itacarobotics/Metis2/doc/motors/17HS24-2004D-E1K/17HS24-2004D-E1K_Torque_Curve.pdf

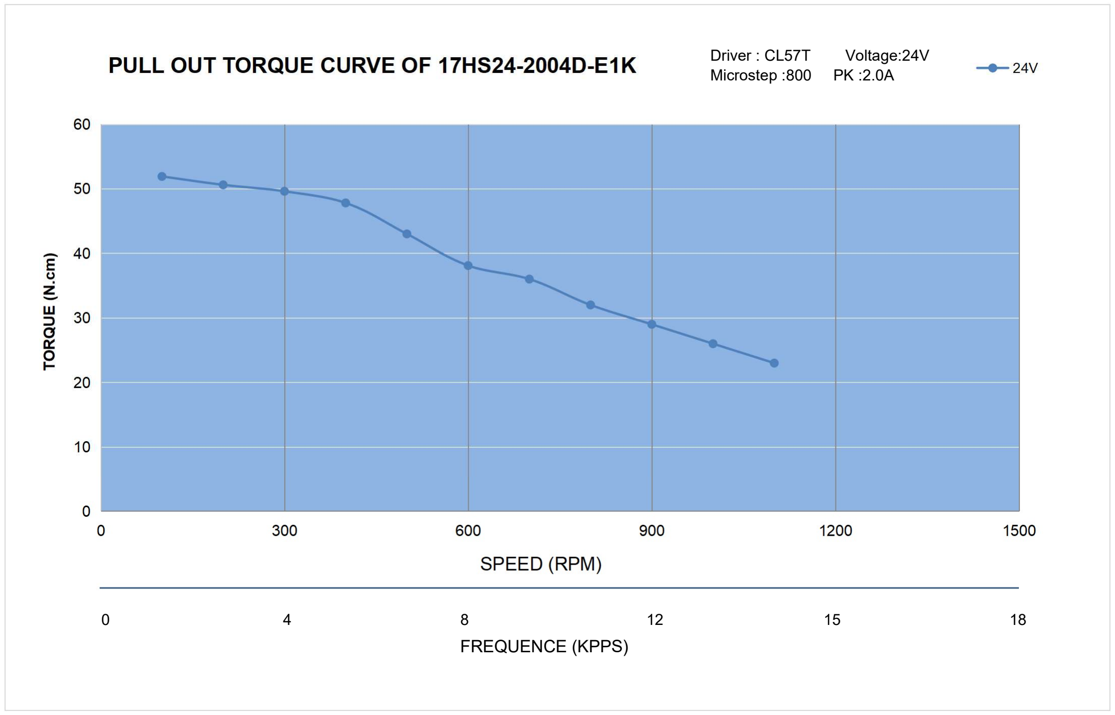
[picture p1: page 1]

Driver : CL57T | Voltage:24V
Microstep :800 | PK :2.0A
0 | 4 | 8 | 12 | 15 | 18
FREQUENCE (KPPS)
