itacarobotics/Metis2/doc/motors/17HS24-2004D-E1K/17HS24-2004D-E1K.pdf

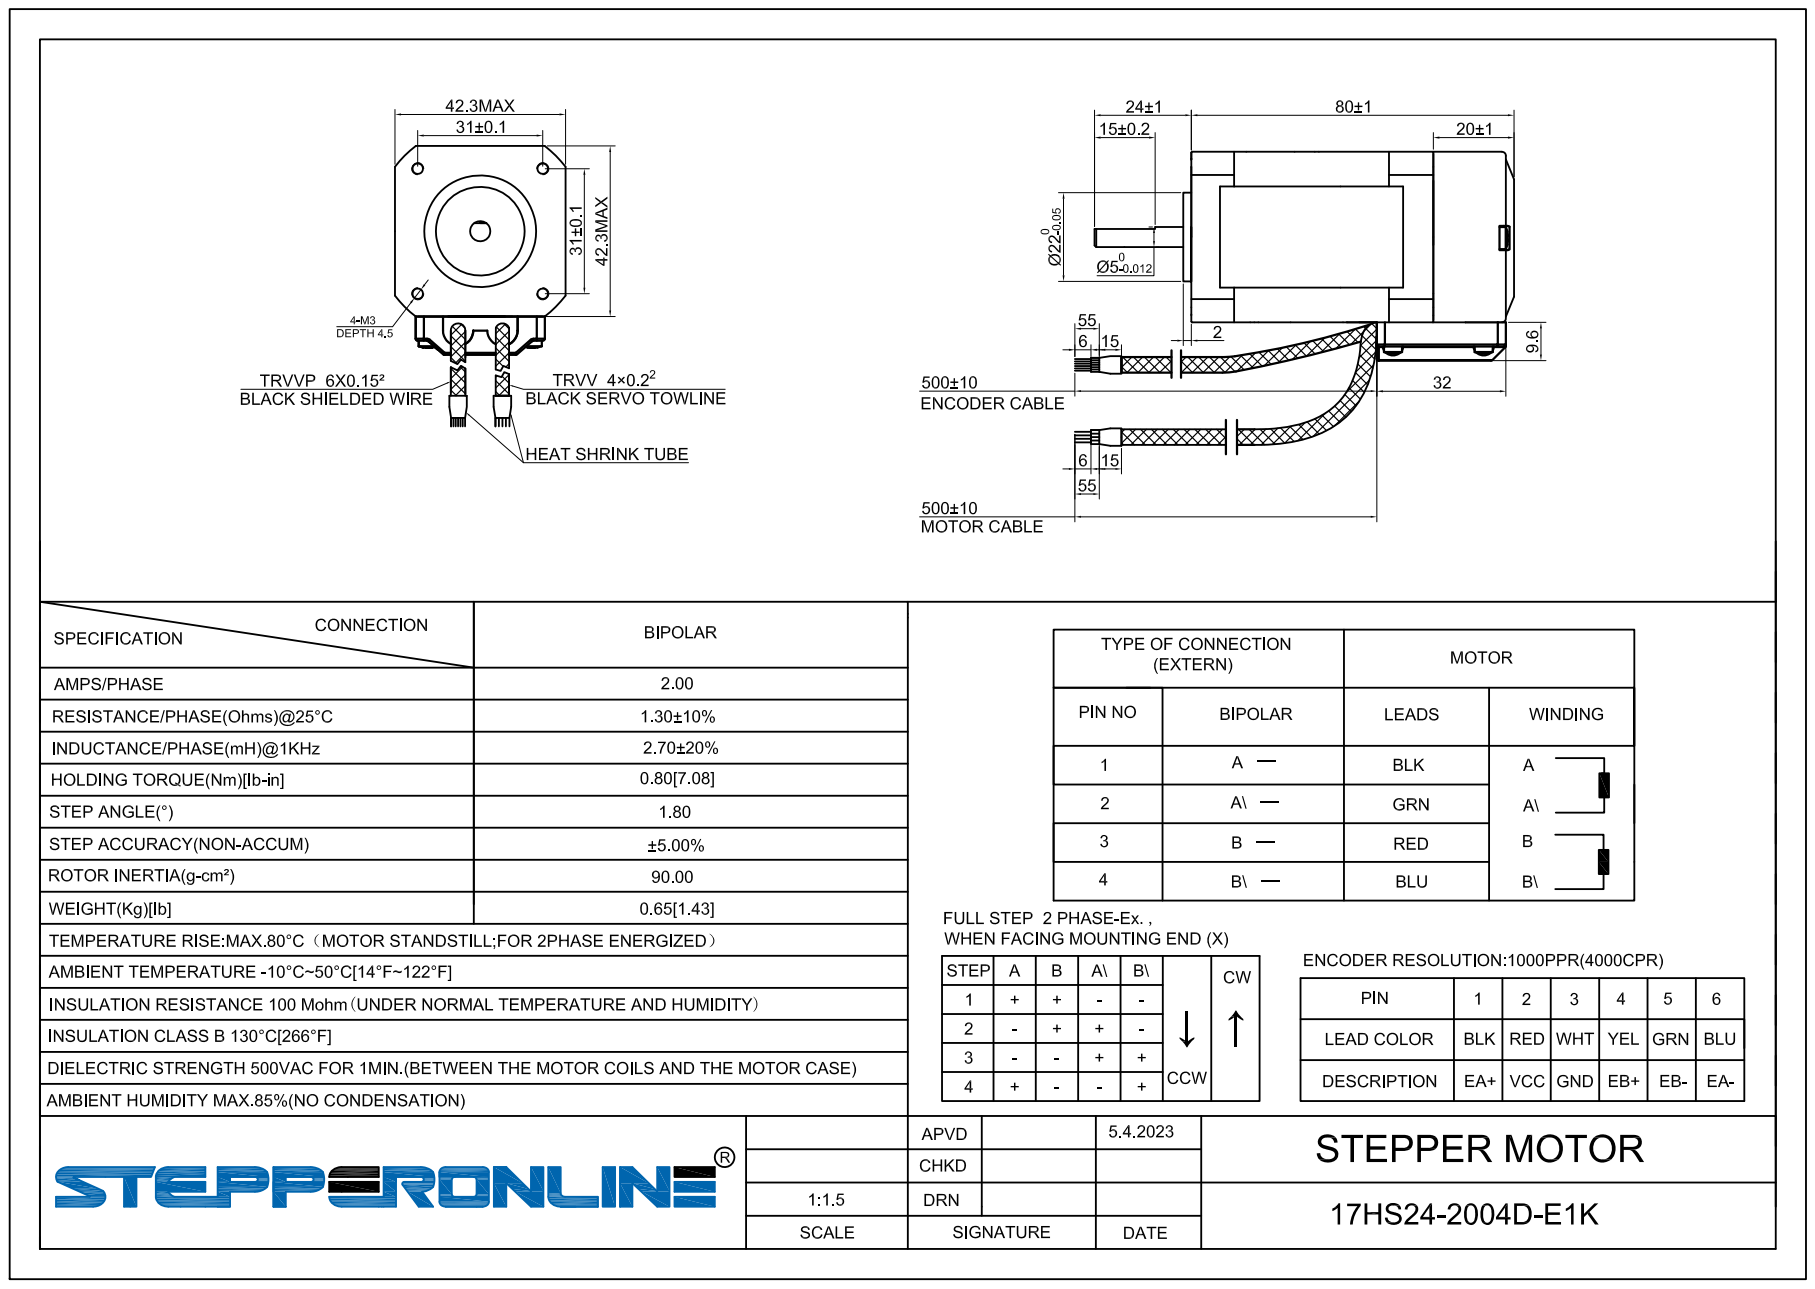
[picture p5: page 1]
